hanshuebner/SmallyMouse2/KiCAD/SmallyMouse2.kicad_sch

## KiCad design KiCAD/SmallyMouse2.kicad_sch (2022-09-16)

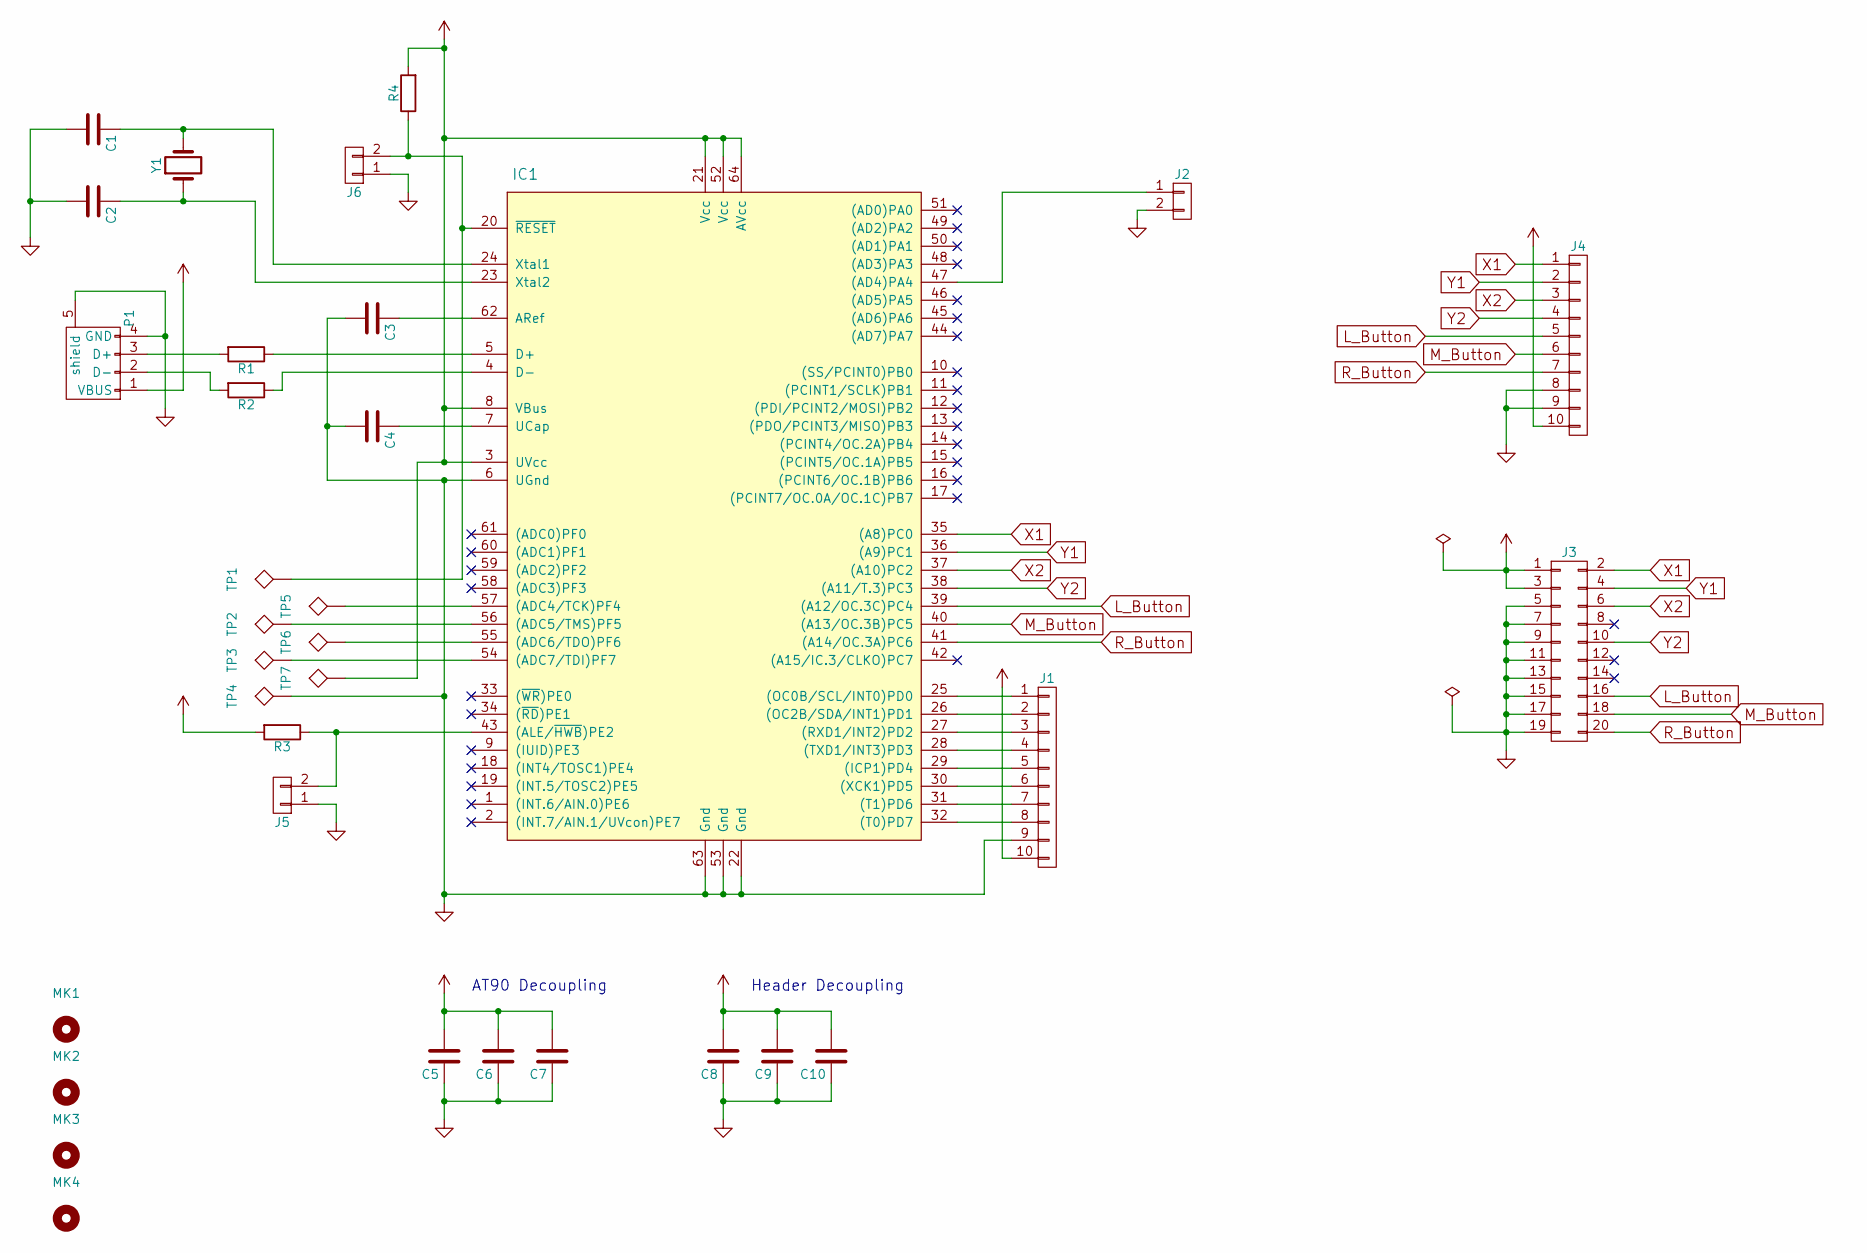
[picture p3: schematic SmallyMouse2.kicad_sch]

Parts:
C1, C2, C3, C4, C5, C6, C7, C8, C9, C10: (no value)
IC1: (no value)
J1, J2, J3, J4, J5, J6: (no value)
MK1, MK2, MK3, MK4: (no value)
P1: (no value)
R1, R2, R3, R4: (no value)
TP1, TP2, TP3, TP4, TP5, TP6, TP7: (no value)
Y1: (no value)

Connections:
L_Button: IC1.39 ((A12/OC.3C)PC4), J3.16, J4.5
M_Button: IC1.40 ((A13/OC.3B)PC5), J3.18, J4.6
unnamed: C1.1, IC1.24 (Xtal1), Y1.2
unnamed: C1.2, C2.2, C3.2, C4.2, C5.1, C5.2, C6.1, C6.2, C7.1, C7.2, C8.1, C8.2, C9.1, C9.2, C10.1, C10.2, IC1.3 (UVcc), IC1.6 (UGnd), IC1.8 (VBus), IC1.21 (Vcc), IC1.22 (Gnd), IC1.52 (Vcc), IC1.53 (Gnd), IC1.63 (Gnd), IC1.64 (AVcc), J1.9, J1.10, J2.2, J3.1, J3.3, J3.5, J3.7, J3.9, J3.11, J3.13, J3.15, J3.17, J3.19, J4.8, J4.9, J4.10, J5.1, J6.1, P1.1 (VBUS), P1.4 (GND), P1.5 (shield), R3.2, R4.2, TP4.1, TP7.1
unnamed: C2.1, IC1.23 (Xtal2), Y1.1
unnamed: C3.1, IC1.62 (ARef)
unnamed: C4.1, IC1.7 (UCap)
unnamed: IC1.4 (D-), R2.1
unnamed: IC1.5 (D+), R1.1
unnamed: IC1.20 (~RESET), J6.2, R4.1, TP1.1
unnamed: IC1.25 ((OC0B/SCL/INT0)PD0), J1.1
unnamed: IC1.26 ((OC2B/SDA/INT1)PD1), J1.2
unnamed: IC1.27 ((RXD1/INT2)PD2), J1.3
unnamed: IC1.28 ((TXD1/INT3)PD3), J1.4
unnamed: IC1.29 ((ICP1)PD4), J1.5
unnamed: IC1.30 ((XCK1)PD5), J1.6
unnamed: IC1.31 ((T1)PD6), J1.7
unnamed: IC1.32 ((T0)PD7), J1.8
unnamed: IC1.43 ((ALE/~HWB)PE2), J5.2, R3.1
unnamed: IC1.47 ((AD4)PA4), J2.1
unnamed: IC1.54 ((ADC7/TDI)PF7), TP3.1
unnamed: IC1.55 ((ADC6/TDO)PF6), TP6.1
unnamed: IC1.56 ((ADC5/TMS)PF5), TP2.1
unnamed: IC1.57 ((ADC4/TCK)PF4), TP5.1
unnamed: P1.2 (D-), R2.2
unnamed: P1.3 (D+), R1.2
R_Button: IC1.41 ((A14/OC.3A)PC6), J3.20, J4.7
X1: IC1.35 ((A8)PC0), J3.2, J4.1
X2: IC1.37 ((A10)PC2), J3.6, J4.3
Y1: IC1.36 ((A9)PC1), J3.4, J4.2
Y2: IC1.38 ((A11/T.3)PC3), J3.10, J4.4

Notes on the sheet:
AT90 Decoupling
Header Decoupling
